igorkll/LGC-Boombox/LGC-Boombox-firmware/winbox_resources/sources/boomUI/apps/files/search.png

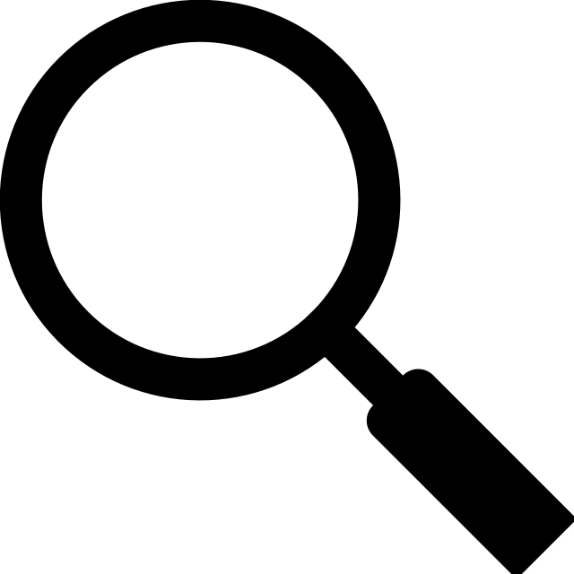
LGC-Boombox-firmware/winbox_resources/sources/boomUI/apps/files/search.png
