igorkll/LGC-Boombox/LGC-Boombox-firmware/winbox_resources/sources/boomUI/apps/music/error.png

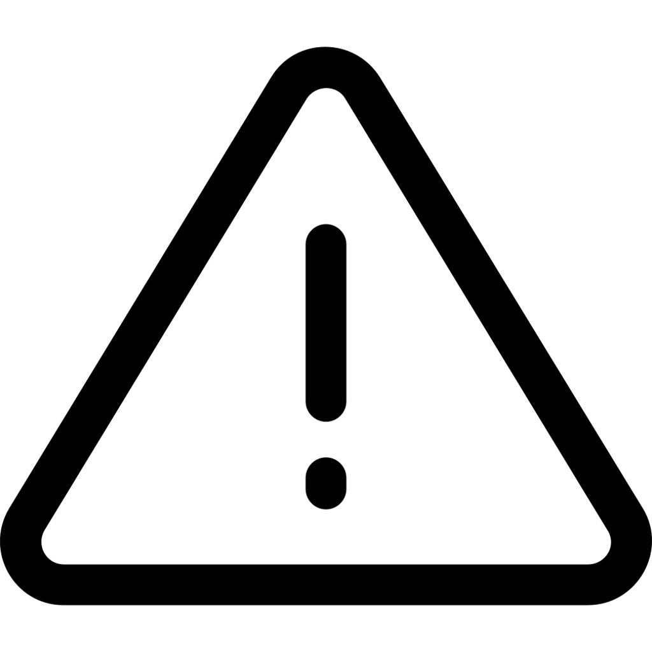
LGC-Boombox-firmware/winbox_resources/sources/boomUI/apps/music/error.png
