igorkll/LGC-Boombox/LGC-Boombox-firmware/winbox_resources/sources/boomUI/apps/music/fullscreen.png

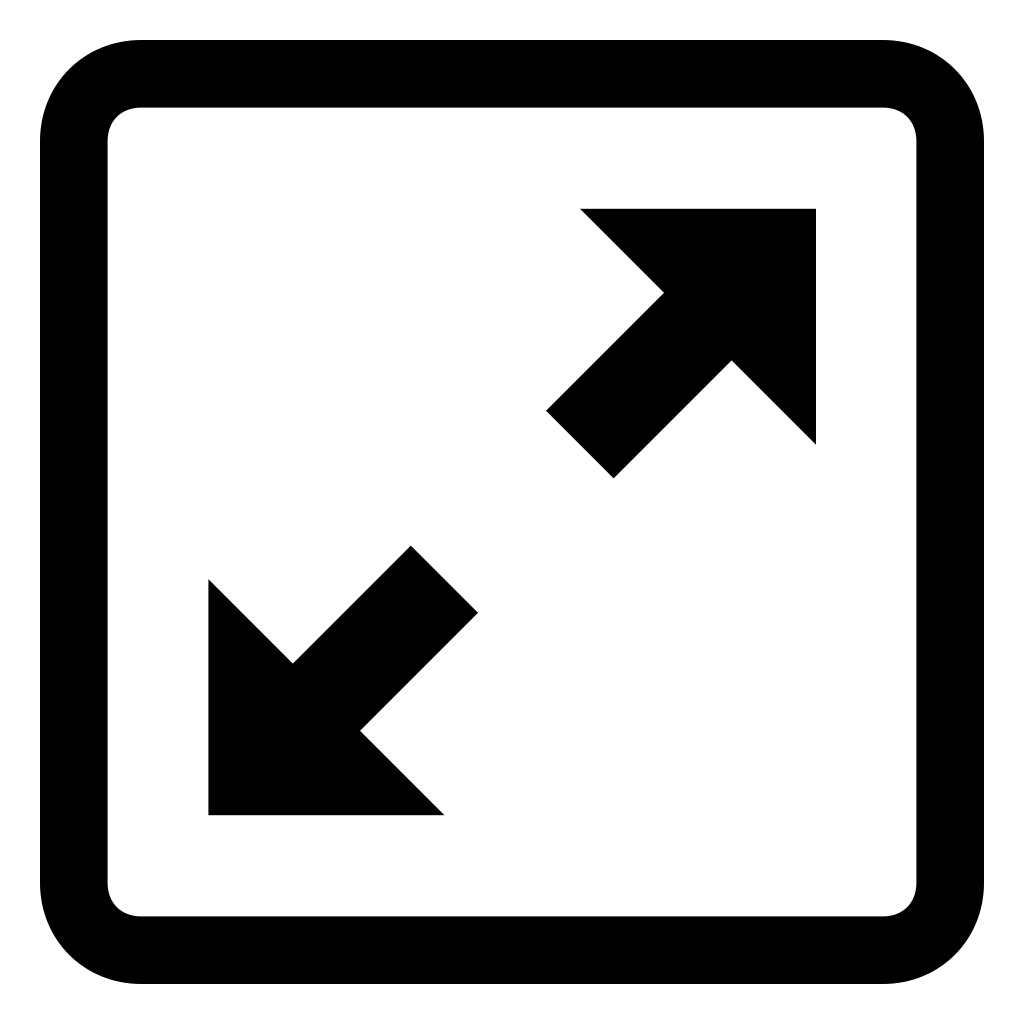
LGC-Boombox-firmware/winbox_resources/sources/boomUI/apps/music/fullscreen.png
