igorkll/LGC-Boombox/LGC-Boombox-firmware/winbox_resources/sources/boomUI/apps/music/loopmode_loop.png

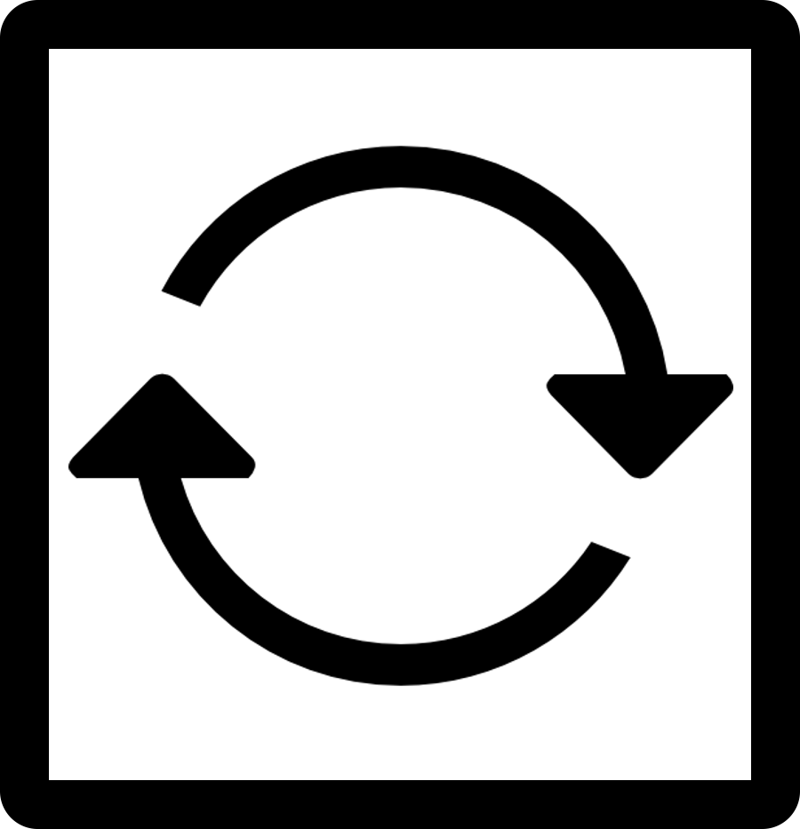
LGC-Boombox-firmware/winbox_resources/sources/boomUI/apps/music/loopmode_loop.png
