igorkll/LGC-Boombox/LGC-Boombox-firmware/winbox_resources/sources/boomUI/apps/music/loopmode_next.png

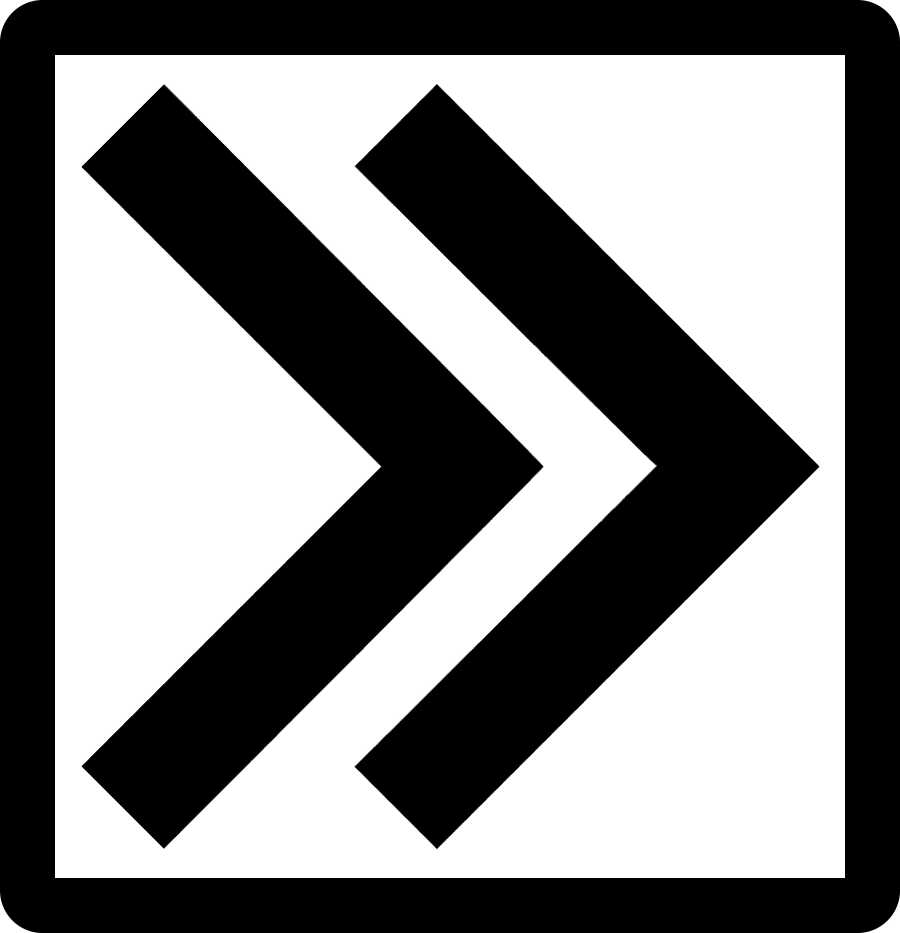
LGC-Boombox-firmware/winbox_resources/sources/boomUI/apps/music/loopmode_next.png
