igorkll/LGC-Boombox/LGC-Boombox-firmware/winbox_resources/sources/boomUI/apps/music/next.png

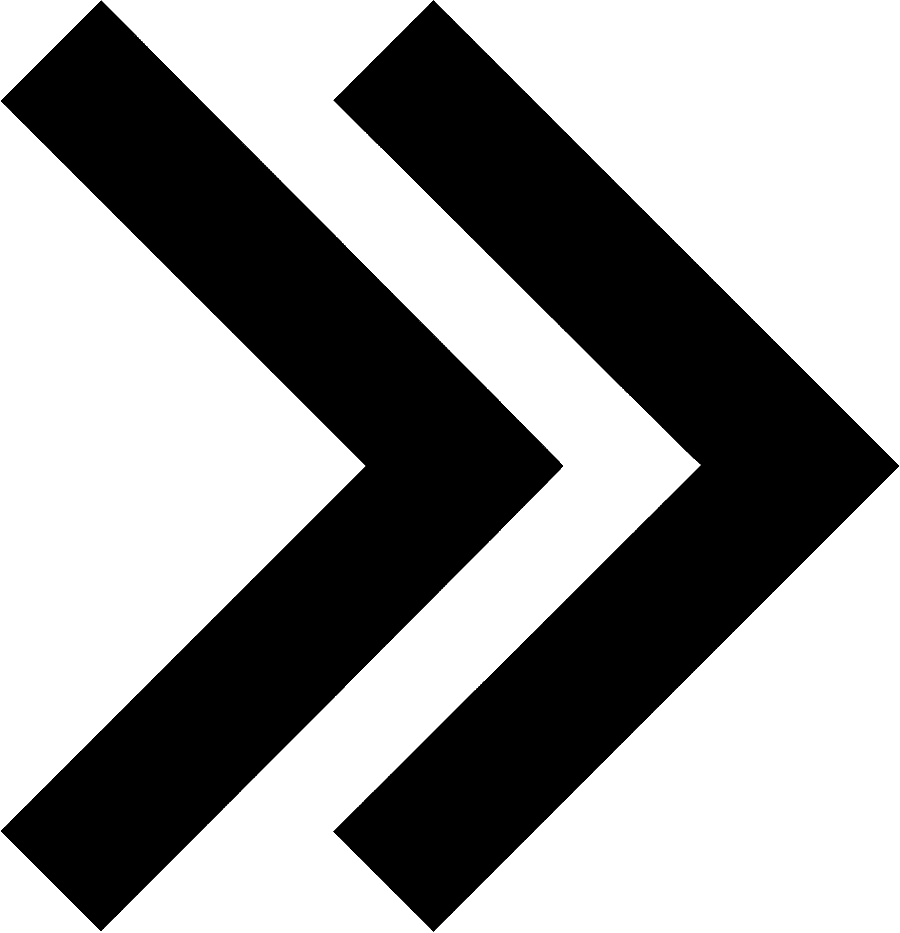
LGC-Boombox-firmware/winbox_resources/sources/boomUI/apps/music/next.png
