igorkll/LGC-Boombox/LGC-Boombox-firmware/winbox_resources/sources/boomUI/apps/music/none.png

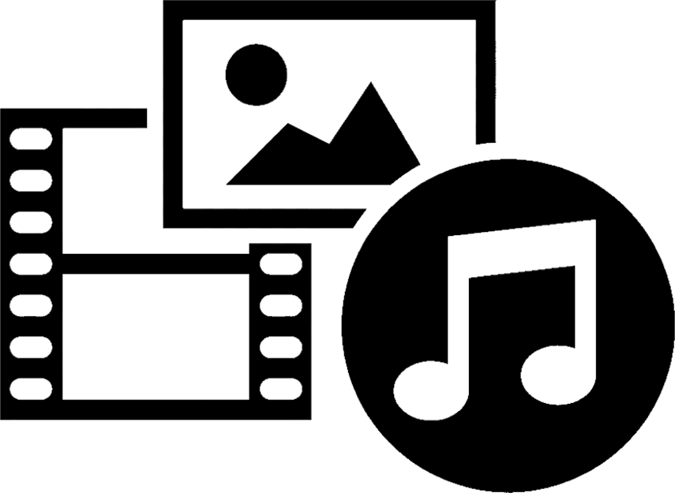
LGC-Boombox-firmware/winbox_resources/sources/boomUI/apps/music/none.png
