igorkll/LGC-Boombox/LGC-Boombox-firmware/winbox_resources/sources/boomUI/apps/music/pause.png

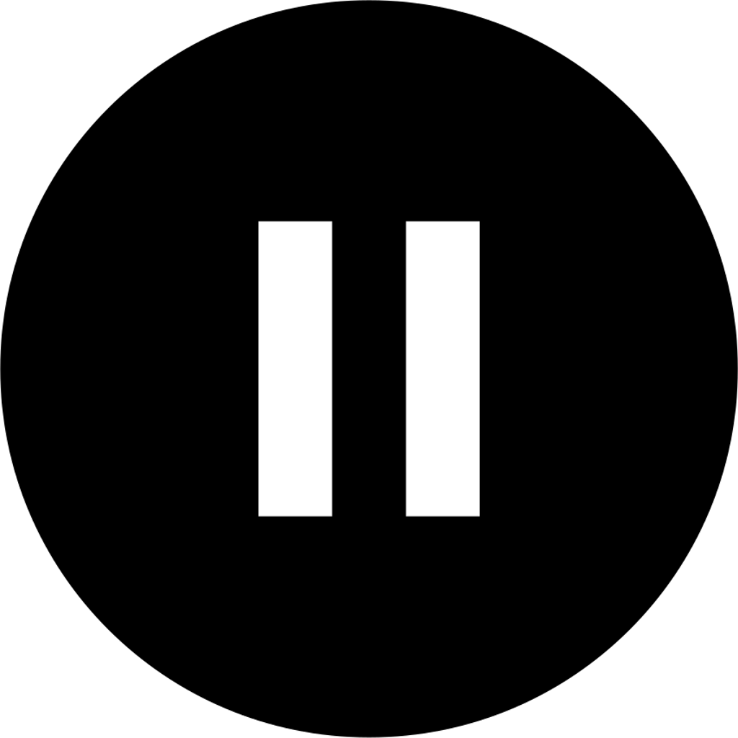
LGC-Boombox-firmware/winbox_resources/sources/boomUI/apps/music/pause.png
