igorkll/LGC-Boombox/LGC-Boombox-firmware/winbox_resources/sources/boomUI/apps/music/play.png

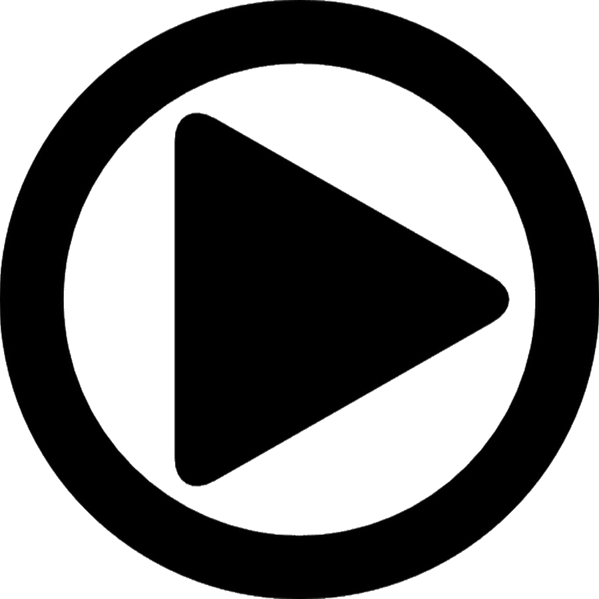
LGC-Boombox-firmware/winbox_resources/sources/boomUI/apps/music/play.png
