igorkll/LGC-Boombox/LGC-Boombox-firmware/winbox_resources/sources/boomUI/apps/music/unfullscreen.png

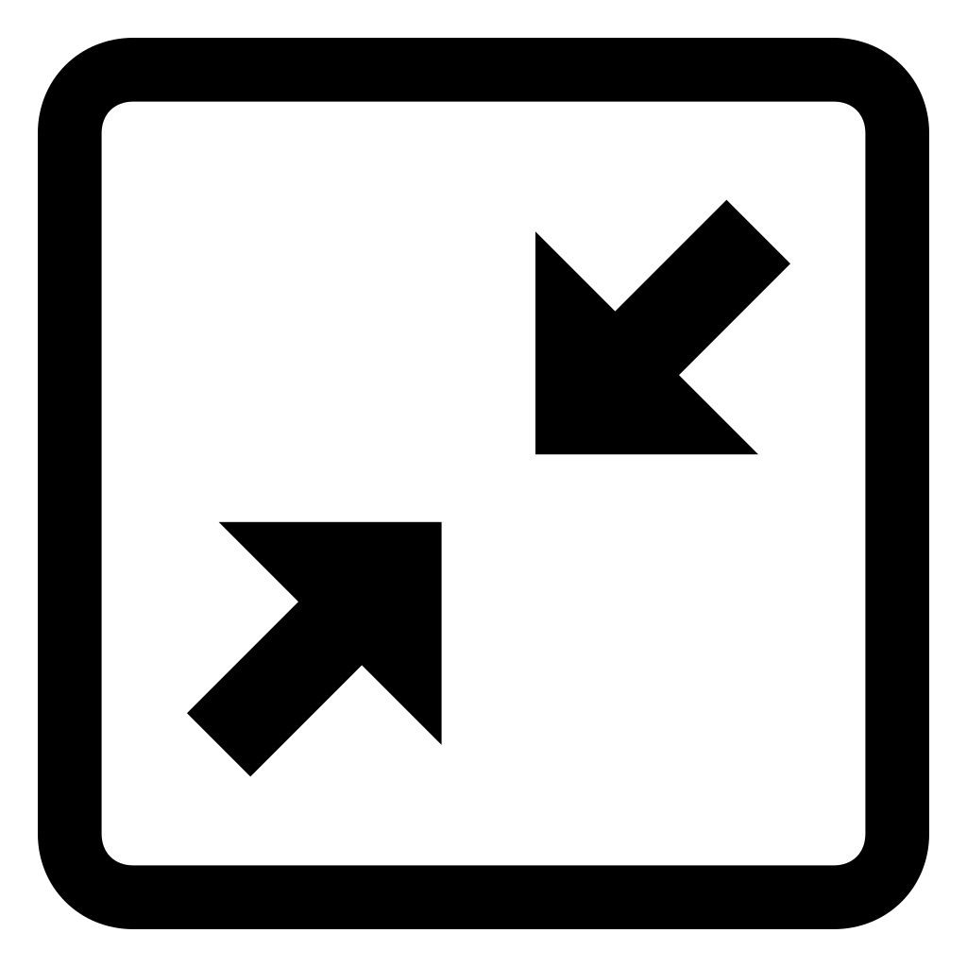
LGC-Boombox-firmware/winbox_resources/sources/boomUI/apps/music/unfullscreen.png
