igorkll/LGC-Boombox/LGC-Boombox-firmware/winbox_resources/sources/boomUI/apps/music/visualizer.png

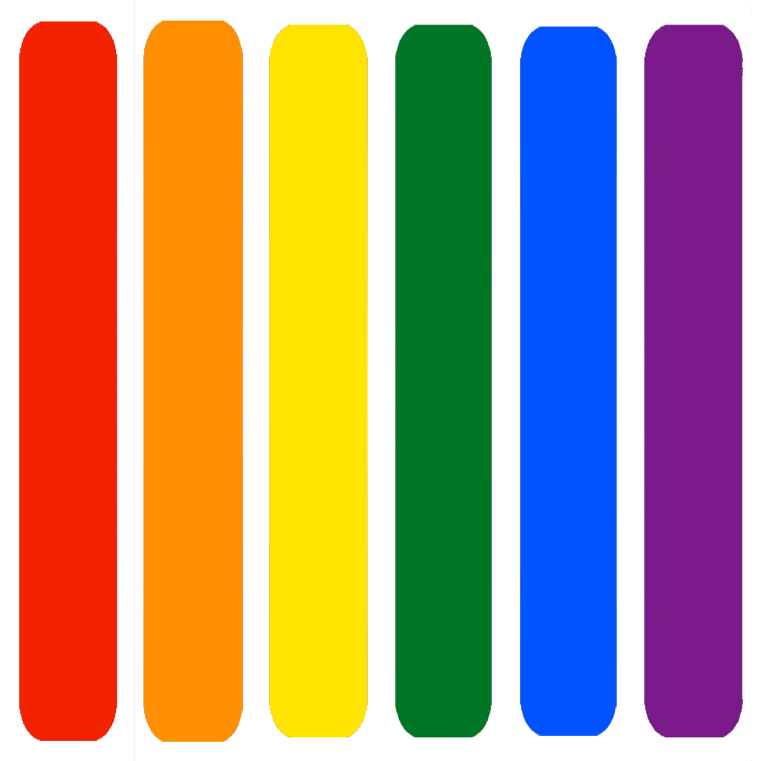
LGC-Boombox-firmware/winbox_resources/sources/boomUI/apps/music/visualizer.png
