igorkll/LGC-Boombox/LGC-Boombox-firmware/winbox_resources/sources/boomUI/wallpapers/41.jpg

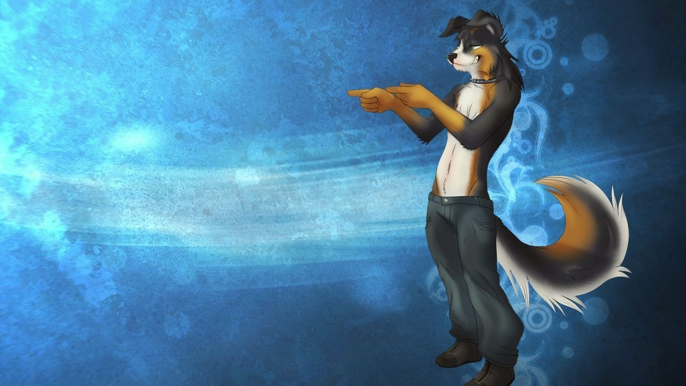
LGC-Boombox-firmware/winbox_resources/sources/boomUI/wallpapers/41.jpg
