igorkll/LGC-Boombox/LGC-Boombox-firmware/winbox_resources/sources/boomUI/wallpapers/44.jpg

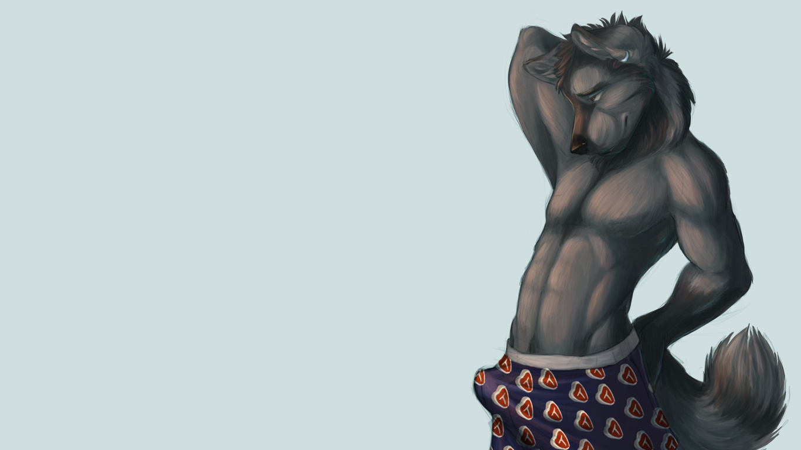
LGC-Boombox-firmware/winbox_resources/sources/boomUI/wallpapers/44.jpg
