igorkll/LGC-Boombox/LGC-Boombox-firmware/winbox_resources/sources/boomUI/wallpapers/45.jpg

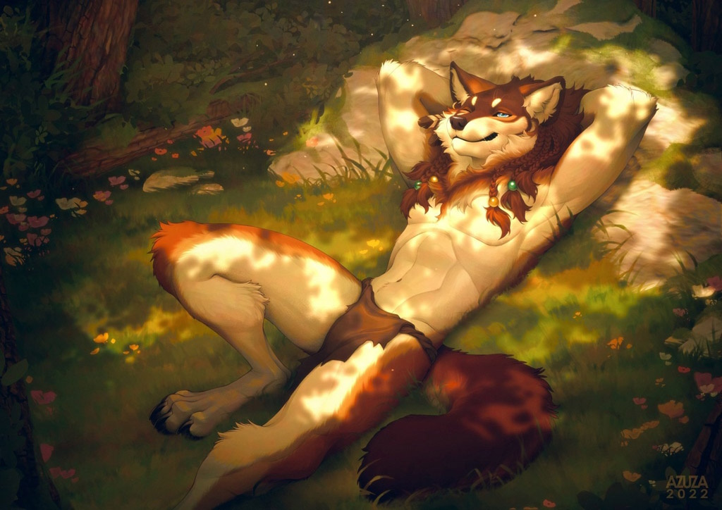
LGC-Boombox-firmware/winbox_resources/sources/boomUI/wallpapers/45.jpg
