igorkll/LGC-Boombox/LGC-Boombox-firmware/winbox_resources/sources/boomUI/wallpapers/46.jpg

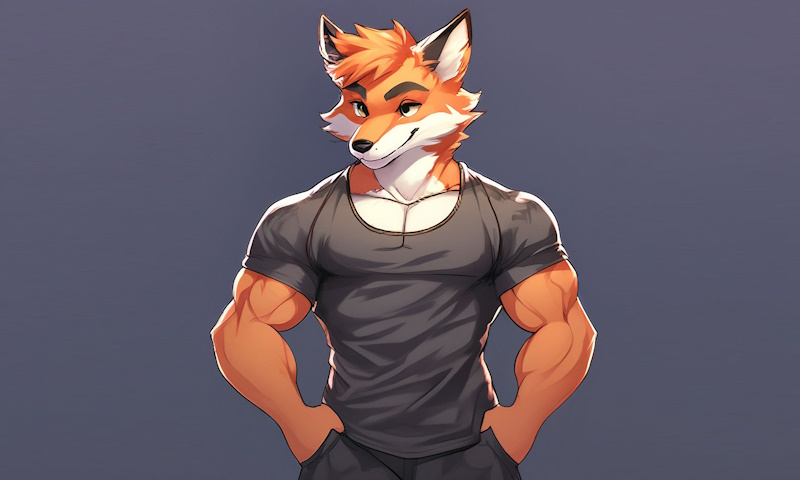
LGC-Boombox-firmware/winbox_resources/sources/boomUI/wallpapers/46.jpg
