igorkll/LGC-Boombox/case/front.scad

$fn = 100;

width = 185;
length = 170;
height = 5;

hole_diameter = 3;
hole_offset = 2.5;

speaker_diameter = 80;
speaker_hole_diameter = 3;
speaker_hole_offset = 6;
speaker_offset = 10;

screen_margin = 1;
screen_width = 121 + screen_margin;
screen_height = 76 + screen_margin;

bracing_width = 30;
bracing_length = 4;
bracing_height = 10;
bracing_offset = 10;
bracing_holo_offset = 10;

logo_hole_offset = 20;
logo_hole_center_offset = 30;

difference() {
    cube([width, length, height]);
    
    // holes
    translate([hole_offset, hole_offset, height / 2]) {
        cylinder(h = height + 1, d = hole_diameter, center = true);
    }
    translate([hole_offset, length - hole_offset, height / 2]) {
        cylinder(h = height + 1, d = hole_diameter, center = true);
    }
    translate([width - hole_offset, hole_offset, height / 2]) {
        cylinder(h = height + 1, d = hole_diameter, center = true);
    }
    translate([width - hole_offset, length - hole_offset, height / 2]) {
        cylinder(h = height + 1, d = hole_diameter, center = true);
    }
    translate([width / 2, hole_offset, height / 2]) {
        cylinder(h = height + 1, d = hole_diameter, center = true);
    }
    translate([width / 2, length - hole_offset, height / 2]) {
        cylinder(h = height + 1, d = hole_diameter, center = true);
    }
    translate([hole_offset, length / 2, height / 2]) {
        cylinder(h = height + 1, d = hole_diameter, center = true);
    }
    
    // speaker
    speaker_x = (speaker_diameter / 2) + speaker_offset;
    speaker_y = length / 2;
    translate([speaker_x, speaker_y, height / 2]) {
        cylinder(h = height + 1, d = speaker_diameter, center = true);
    }
    
    // speaker holes
    local_speaker_hole_offset = ((speaker_diameter / 2) + speaker_hole_offset) / sqrt(2);
    translate([speaker_x + local_speaker_hole_offset, speaker_y + local_speaker_hole_offset, height / 2]) {
        cylinder(h = height + 1, d = speaker_hole_diameter, center = true);
    }
    translate([speaker_x + local_speaker_hole_offset, speaker_y - local_speaker_hole_offset, height / 2]) {
        cylinder(h = height + 1, d = speaker_hole_diameter, center = true);
    }
    translate([speaker_x - local_speaker_hole_offset, speaker_y + local_speaker_hole_offset, height / 2]) {
        cylinder(h = height + 1, d = speaker_hole_diameter, center = true);
    }
    translate([speaker_x - local_speaker_hole_offset, speaker_y - local_speaker_hole_offset, height / 2]) {
        cylinder(h = height + 1, d = speaker_hole_diameter, center = true);
    }
    
    // logo hole
    translate([width - logo_hole_center_offset, logo_hole_offset, height / 2]) {
        cylinder(h = height + 1, d = hole_diameter, center = true);
    }
    translate([width - logo_hole_center_offset, length - logo_hole_offset, height / 2]) {
        cylinder(h = height + 1, d = hole_diameter, center = true);
    }
    
    // screen
    translate([width, length / 2, height / 2]) {
        cube([screen_width, screen_height, height + 1], center = true);
    }
}

module bracing(pos) {
    difference() {
        translate(pos) {    
            cube([bracing_length, bracing_width, bracing_height], center = true);
        }
        
        translate([pos[0], pos[1], pos[2]]) {
            rotate([0, 90, 0]) {
                cylinder(h = bracing_length + 1, d = hole_diameter, center = true);
            }
        }
        
        translate([pos[0], pos[1] + bracing_holo_offset, pos[2]]) {
            rotate([0, 90, 0]) {
                cylinder(h = bracing_length + 1, d = hole_diameter, center = true);
            }
        }
        
        translate([pos[0], pos[1] - bracing_holo_offset, pos[2]]) {
            rotate([0, 90, 0]) {
                cylinder(h = bracing_length + 1, d = hole_diameter, center = true);
            }
        }
    }
}

bracing([width - bracing_length / 2, (bracing_width / 2) + bracing_offset, height + bracing_height / 2]);
bracing([width - bracing_length / 2, (length - bracing_width / 2) - bracing_offset, height + bracing_height / 2]);
