igorkll/LGC-Boombox/esp32c3_firmware/main/main.h

#pragma once

#include <stdint.h>
#include <stdlib.h>
#include <stdio.h>
#include <math.h>
#include <string.h>

#include <esp_log.h>
#include <esp_err.h>

#include <freertos/FreeRTOS.h>
#include <freertos/task.h>

#include <driver/uart.h>
#include <driver/gpio.h>

#include <driver/usb_serial_jtag.h>
